marcellodash/ossc/diy-audio/installation/installation_ae_01-v1.5.png

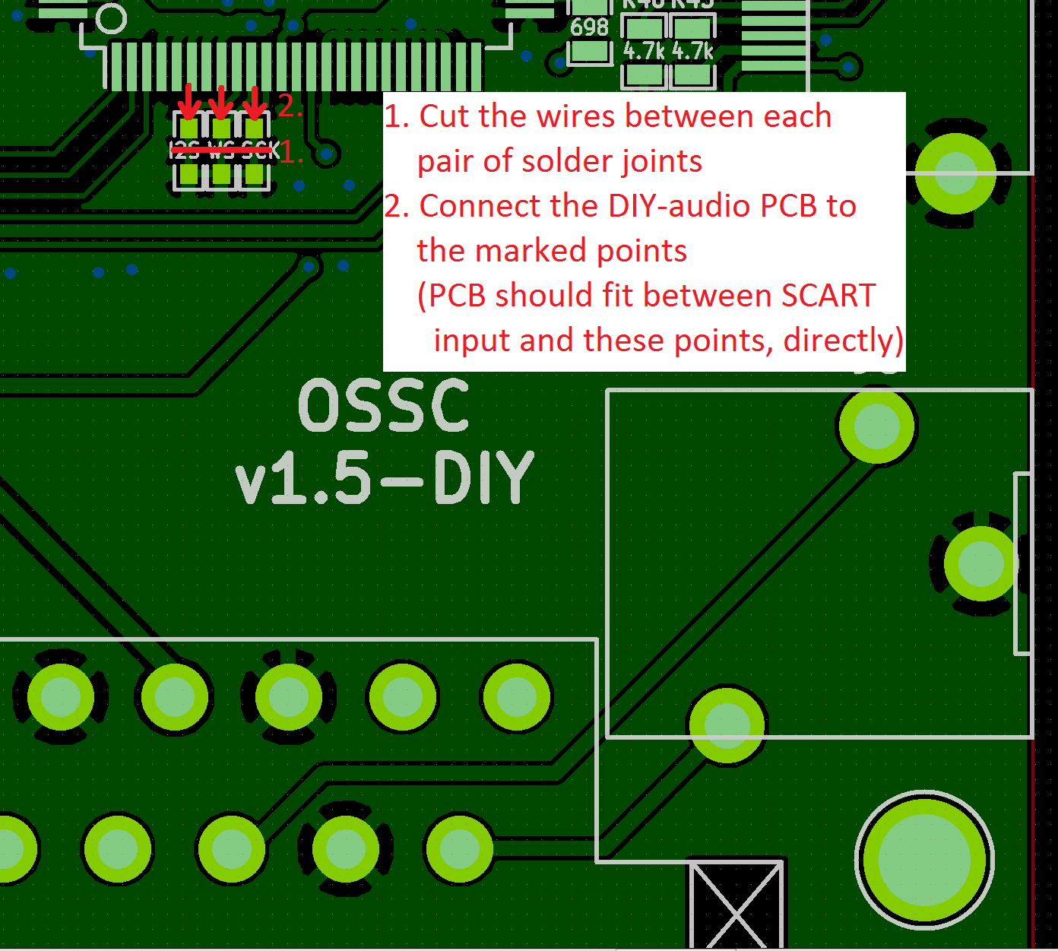
diy-audio/installation/installation_ae_01-v1.5.png
