marcellodash/ossc/diy-audio/installation/installation_ae_03.JPG

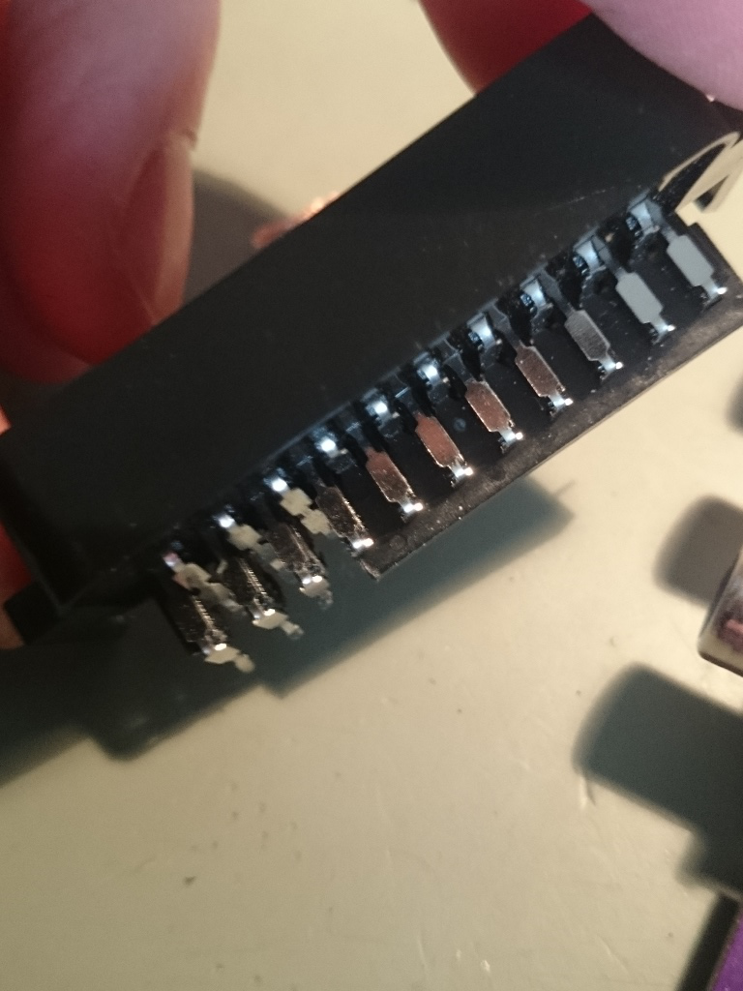
diy-audio/installation/installation_ae_03.JPG
