marcellodash/ossc/diy-audio/installation/installation_ae_04.JPG

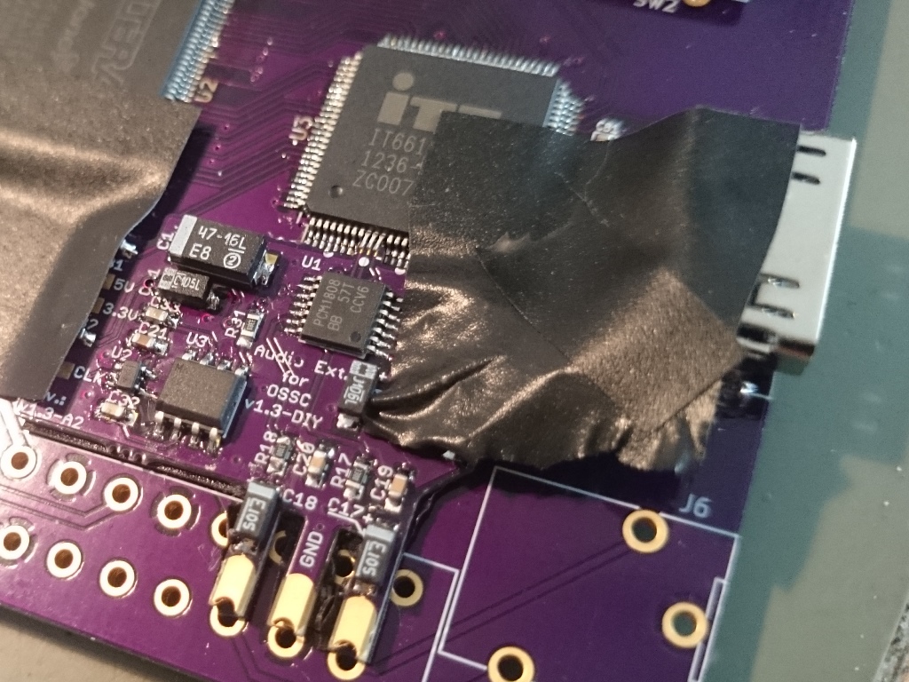
diy-audio/installation/installation_ae_04.JPG
