marcellodash/ossc/diy-audio/installation/installation_ae_05.JPG

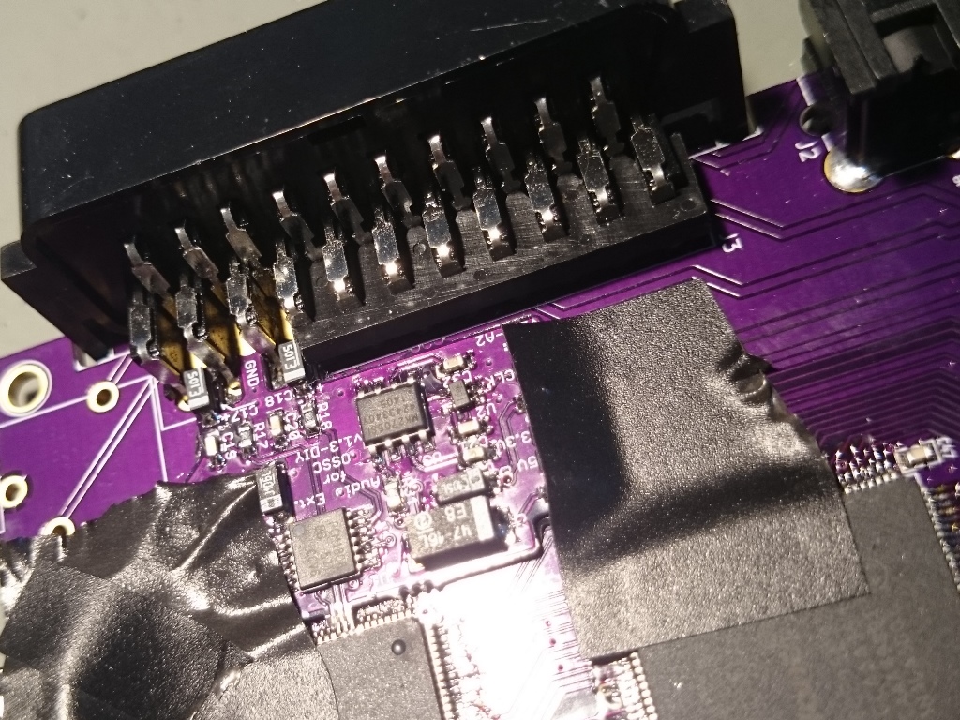
diy-audio/installation/installation_ae_05.JPG
