marcellodash/ossc/diy-audio/installation/installation_ae_06-v1.5.JPG

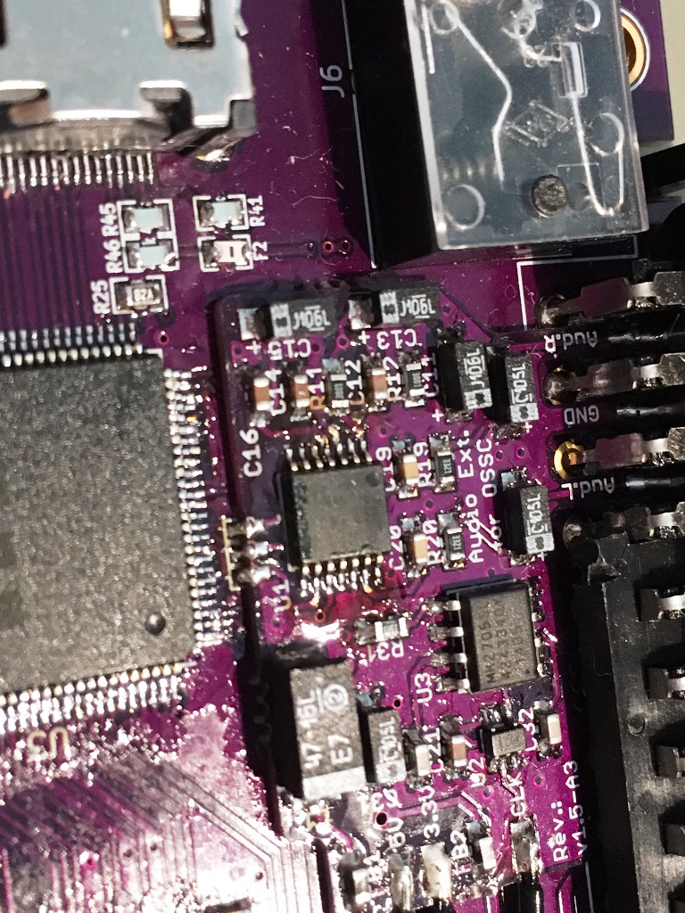
diy-audio/installation/installation_ae_06-v1.5.JPG
