marcellodash/ossc/diy-audio/installation/installation_mclk_10-v1.5.JPG

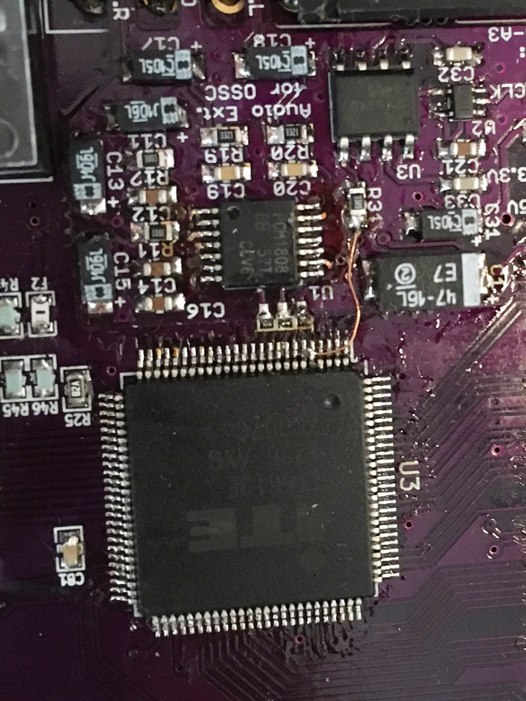
diy-audio/installation/installation_mclk_10-v1.5.JPG
