marcellodash/ossc/software/sys_controller/ossc/av_controller.h

//
// Copyright (C) 2015-2016  Markus Hiienkari <mhiienka@niksula.hut.fi>
//
// This file is part of Open Source Scan Converter project.
//
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

#ifndef AV_CONTROLLER_H_
#define AV_CONTROLLER_H_

#include "avconfig.h"
#include "sysconfig.h"

// sys_ctrl bits
#define LT_ACTIVE   (1<<15)
#define LT_ARMED    (1<<14)
#define LT_MODE_OFFS    12
#define SD_SPI_SS_N (1<<7)
#define LCD_CS_N    (1<<6)
#define LCD_RS      (1<<5)
#define LCD_BL      (1<<4)
#define VIDGEN_OFF  (1<<1)
#define AV_RESET_N  (1<<0)

#define LT_CTRL_MASK    0xf000

// HDMI_TX definitions
#define HDMITX_MODE_MASK            0x00040000

#define TX_PIXELREP_DISABLE         0
#define TX_PIXELREP_2X              1
#define TX_PIXELREP_4X              3

// FPGA macros
#define FPGA_V_MULTMODE_1X          0
#define FPGA_V_MULTMODE_2X          1
#define FPGA_V_MULTMODE_3X          2
#define FPGA_V_MULTMODE_4X          3
#define FPGA_V_MULTMODE_5X          4

#define FPGA_H_MULTMODE_FULLWIDTH   0
#define FPGA_H_MULTMODE_ASPECTFIX   1
#define FPGA_H_MULTMODE_OPTIMIZED   2

#define FPGA_SCANLINEMODE_OFF       0
#define FPGA_SCANLINEMODE_H         1
#define FPGA_SCANLINEMODE_V         2
#define FPGA_SCANLINEMODE_ALT       3

static const char *avinput_str[] = { "Test pattern", "AV1: RGBS", "AV1: RGsB", "AV1: YPbPr", "AV2: YPbPr", "AV2: RGsB", "AV3: RGBHV", "AV3: RGBS", "AV3: RGsB", "AV3: YPbPr", "Last used" };

typedef enum {
    AV_KEEP         = 0,
    AV1_RGBs        = 1,
    AV1_RGsB        = 2,
    AV1_YPBPR       = 3,
    AV2_YPBPR       = 4,
    AV2_RGsB        = 5,
    AV3_RGBHV       = 6,
    AV3_RGBs        = 7,
    AV3_RGsB        = 8,
    AV3_YPBPR       = 9,
    AV_LAST         = 10
} avinput_t;

// In reverse order of importance
typedef enum {
    NO_CHANGE           = 0,
    INFO_CHANGE         = 1,
    MODE_CHANGE         = 2,
    TX_MODE_CHANGE      = 3,
    ACTIVITY_CHANGE     = 4
} status_t;

typedef enum {
    TX_HDMI             = 0,
    TX_DVI              = 1
} tx_mode_t;

//TODO: transform binary values into flags
typedef struct {
    alt_u32 totlines;
    alt_u32 clkcnt;
    alt_u8 progressive;
    alt_u8 macrovis;
    alt_8 id;
    alt_u8 sync_active;
    alt_u8 fpga_vmultmode;
    alt_u8 fpga_hmultmode;
    alt_u8 tx_pixelrep;
    alt_u8 hdmitx_pixr_ifr;
    alt_u8 sample_mult;
    alt_u8 sample_sel;
    alt_u8 hsync_cut;
    mode_flags target_lm;
    avinput_t avinput;
    // Current configuration
    avconfig_t cc;
} avmode_t;

inline void lcd_write_menu();
inline void lcd_write_status();

void vm_select();
void vm_tweak(alt_u16 v);
int load_profile();
int save_profile();

int latency_test();

#endif
