marcellodash/ossc/software/sys_controller_bsp/HAL/inc/sys/alt_log_printf.h

/*  alt_log_printf.h
 *
 *  ALT_LOG is designed to provide extra logging/debugging messages from HAL
 *  through a different port than stdout.  It is enabled by the ALT_LOG_ENABLE
 *  define, which needs to supplied at compile time.  When logging is turned off, 
 *  code size is unaffected.  Thus, this should be transparent to the user
 *  when it is not actively turned on, and should not affect projects in any way.
 *
 *  There are macros sprinkled within different components, such as the jtag uart 
 *  and timer, in the HAL code.  They are always named ALT_LOG_<name>, and can be
 *  safely ignored if ALT_LOG is turned off. 
 *
 *  To turn on ALT_LOG, ALT_LOG_ENABLE must be defined, and ALT_LOG_PORT_TYPE and
 *  ALT_LOG_PORT_BASE must be set in system.h.  This is done through editing 
 *  <project>.ptf, by editing the alt_log_port_type & alt_log_port_base settings.
 *  See the documentation html file for examples.
 *
 *  When it is turned on, it will output extra HAL messages to a port specified
 *  in system.h.  This can be a UART or JTAG UART port.  By default it will 
 *  output boot messages, detailing every step of the boot process.  
 *
 *  Extra logging is designed to be enabled by flags, which are defined in 
 *  alt_log_printf.c.  The default value is that all flags are off, so only the
 *  boot up logging messages show up.  ALT_LOG_FLAGS can be set to enable certain
 *  groupings of flags, and that grouping is done in this file.  Each flag can 
 *  also be overridden with a -D at compile time.
 *
 *  This header file includes the necessary prototypes for using the alt_log
 *  functions.  It also contains all the macros that are used to remove the code
 *  from alt log is turned off.  Also, the macros in other HAL files are defined 
 *  here at the bottom.  These macros all call some C function that is in 
 *  alt_log_printf.c.
 *
 *  The logging has functions for printing in C (ALT_LOG_PRINTF) and in assembly
 *  (ALT_LOG_PUTS).  This was needed because the assembly printing occurs before
 *  the device is initialized.  The assembly function corrupts register R4-R7, 
 *  which are not used in the normal boot process.  For this reason, do not call
 *  the assembly function in C.
 *
 *  author: gkwan 
 */


#ifndef __ALT_LOG_PRINTF_H__
#define __ALT_LOG_PRINTF_H__

#include <system.h>
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
